MP120TC/DFS69/STEP_Files/Carrier_Plate_6x8.step

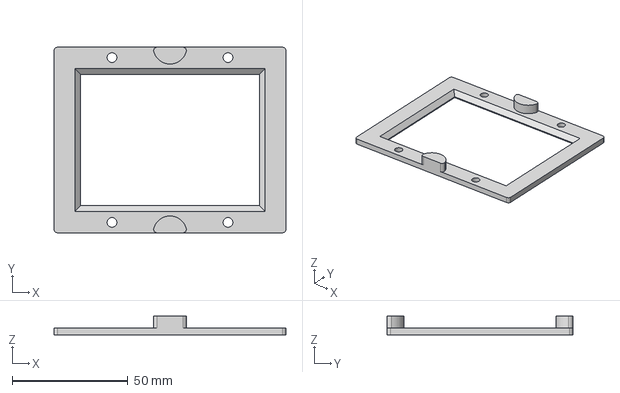
[picture p17: CAD file, 2023-02-04]
STEP_Files/Carrier_Plate_6x8.step
100.0 x 80.0 x 8.00 mm
