MP120TC/DFS69/STEP_Files/Carrier_Plate_645.step

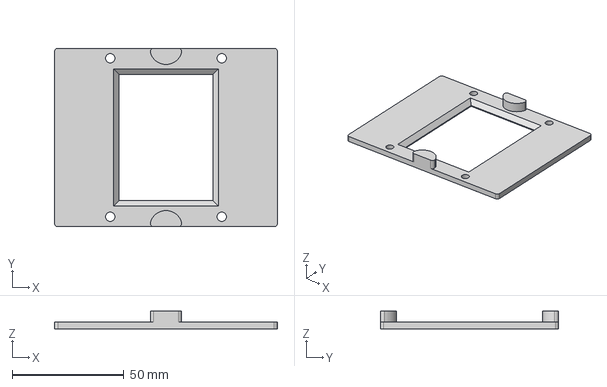
[picture p20: CAD file, 2023-02-04]
STEP_Files/Carrier_Plate_645.step
100.0 x 80.0 x 8.00 mm
