MP120TC/DFS69/STEP_Files/Carrier_Base_6x7.step

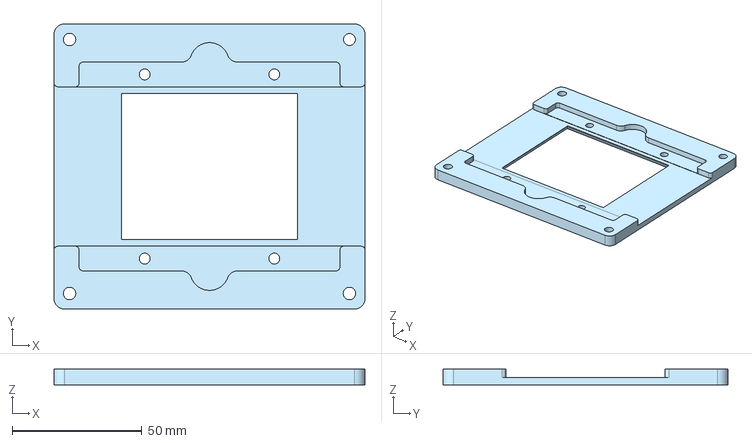
[picture p22: CAD file, 2023-02-04]
STEP_Files/Carrier_Base_6x7.step
120.0 x 110.0 x 6.00 mm
